LostCacher/osmofresh-quellapro-reverse-engineering/Pictures/Hauptplatine_IC1_28Pin.png

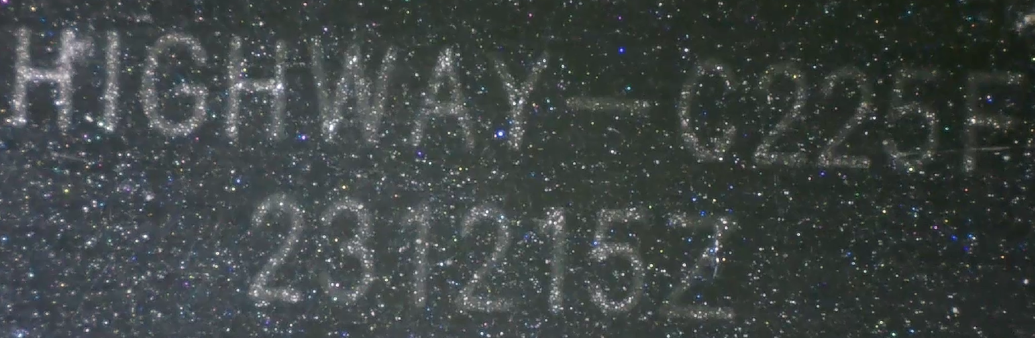
Pictures/Hauptplatine_IC1_28Pin.png
