LostCacher/osmofresh-quellapro-reverse-engineering/Pictures/Hauptplatine_U4_16Pin.png

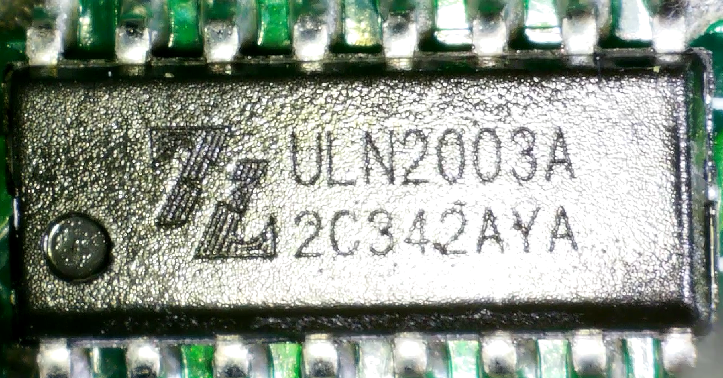
Pictures/Hauptplatine_U4_16Pin.png
