LostCacher/osmofresh-quellapro-reverse-engineering/KiCAD/OsmoFresh_Quella_PRO/MainPCB.5Vdc.kicad_sch

## KiCad design KiCAD/OsmoFresh_Quella_PRO/MainPCB.5Vdc.kicad_sch (2026-08-21, an earlier design)

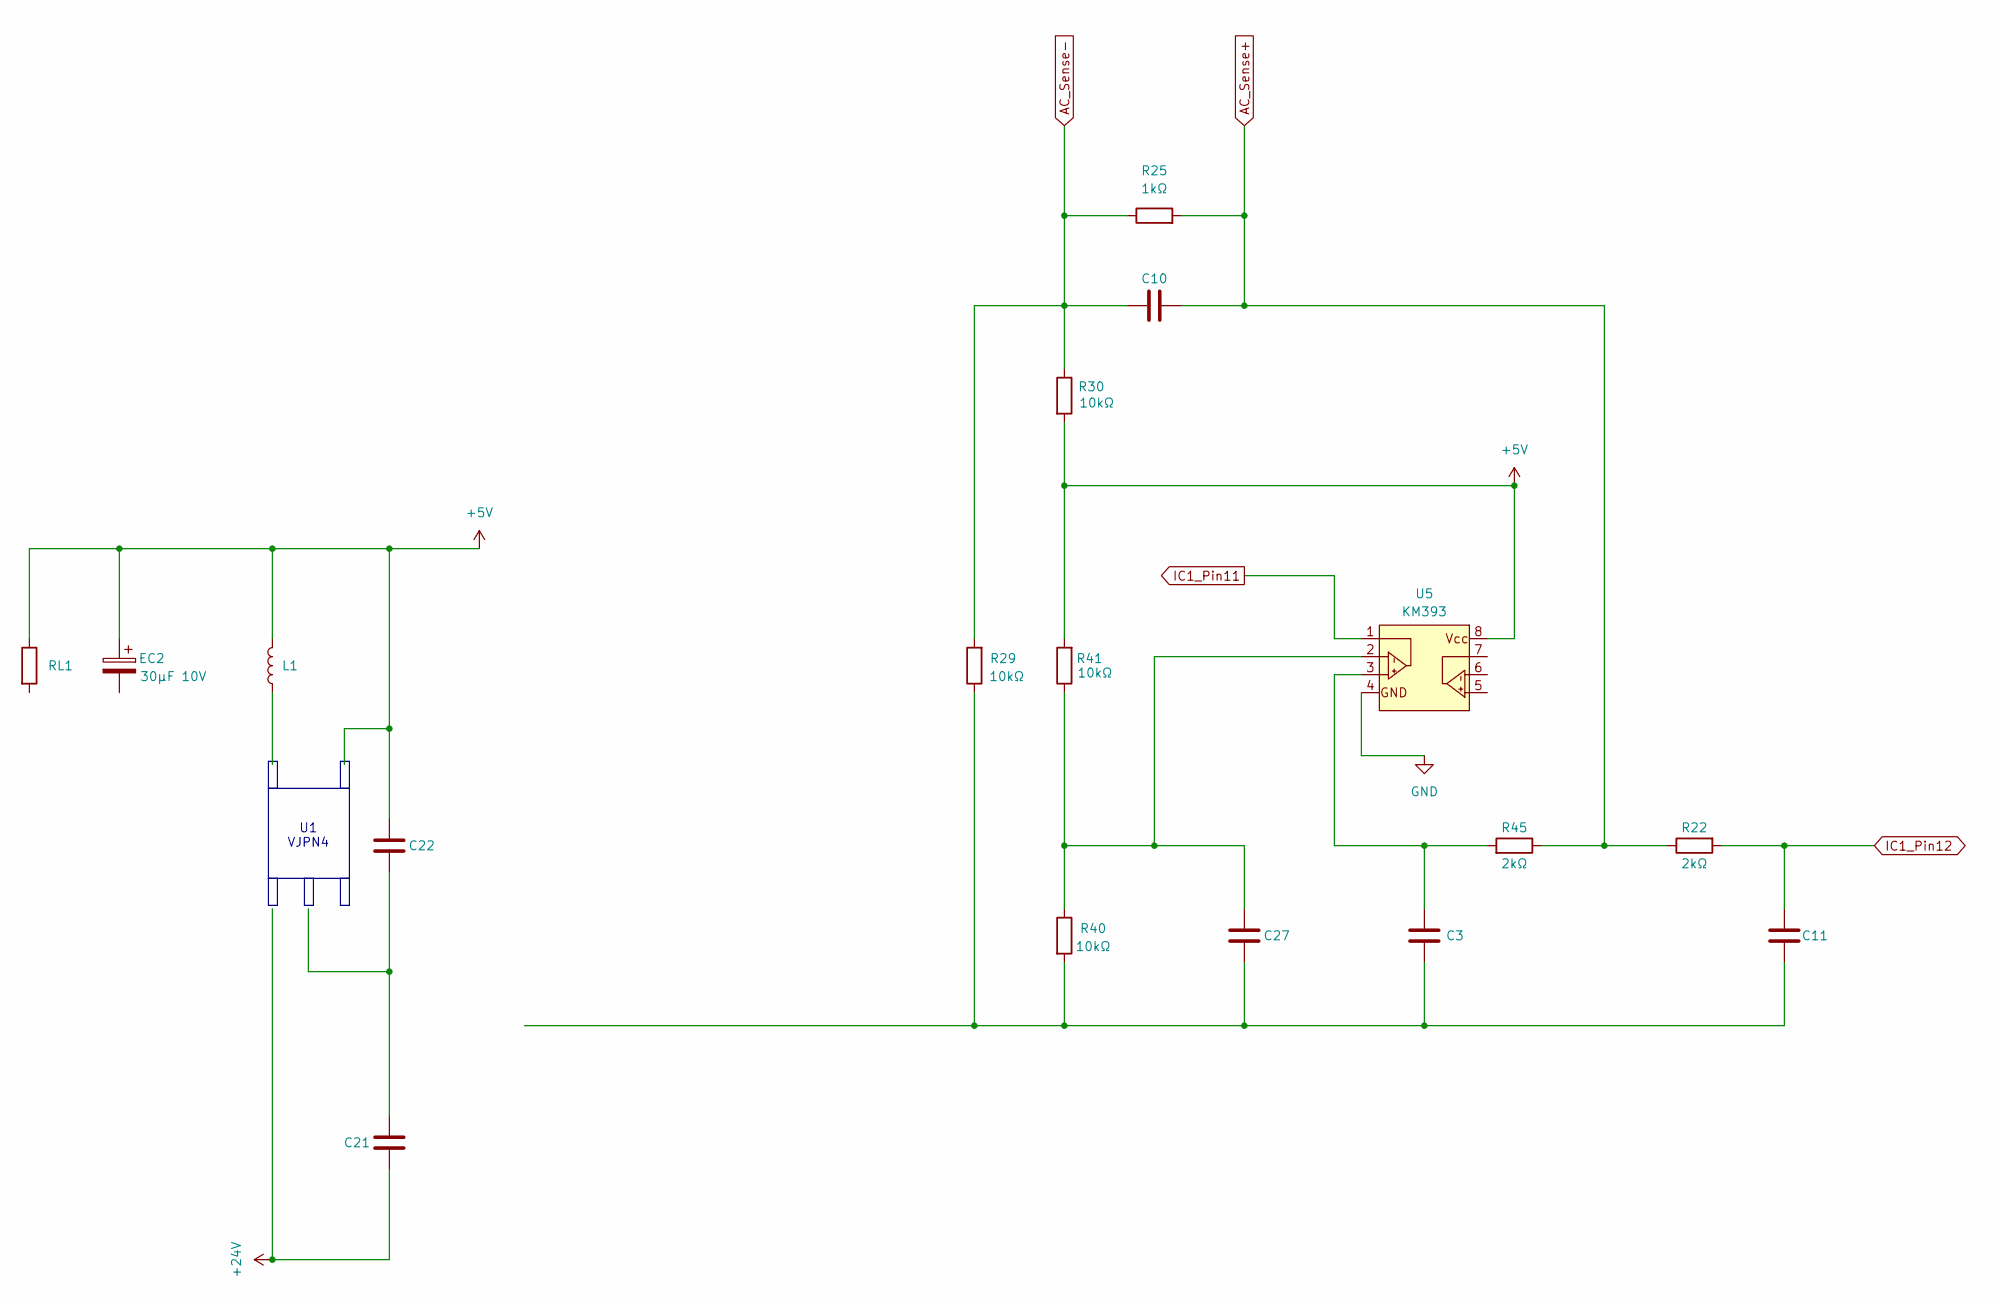
[picture p14: schematic MainPCB.5Vdc.kicad_sch]

Parts:
C3, C11: C
C10, C21, C22, C27: unkown
EC2: 30µF 10V
L1: (no value)
R22, R45: 2kΩ
R25: 1kΩ
R29, R30, R40, R41: 10kΩ
RL1: (no value)
U5: KM393

Connections:
+5V: C22.2, EC2.1, L1.2, R30.2, R41.2, RL1.1, U5.8
+24V: C21.2
AC_Sense+: C10.1, R22.1, R25.2, R45.1
AC_Sense-: C10.2, R25.1, R29.2, R30.1
GND: U5.4
IC1_Pin11: U5.1
IC1_Pin12: C11.1, R22.2
unnamed: C3.1, R45.2, U5.3
unnamed: C3.2, C11.2, C27.1, R29.1, R40.2
unnamed: C21.1, C22.1
unnamed: C27.2, R40.1, R41.1, U5.2

Notes on the sheet:
U1 VJPN4
