LostCacher/osmofresh-quellapro-reverse-engineering/KiCAD/OsmoFresh_Quella_PRO/MainPCB.24Vdc.kicad_sch

## KiCad design KiCAD/OsmoFresh_Quella_PRO/MainPCB.24Vdc.kicad_sch (2026-08-21, an earlier design)

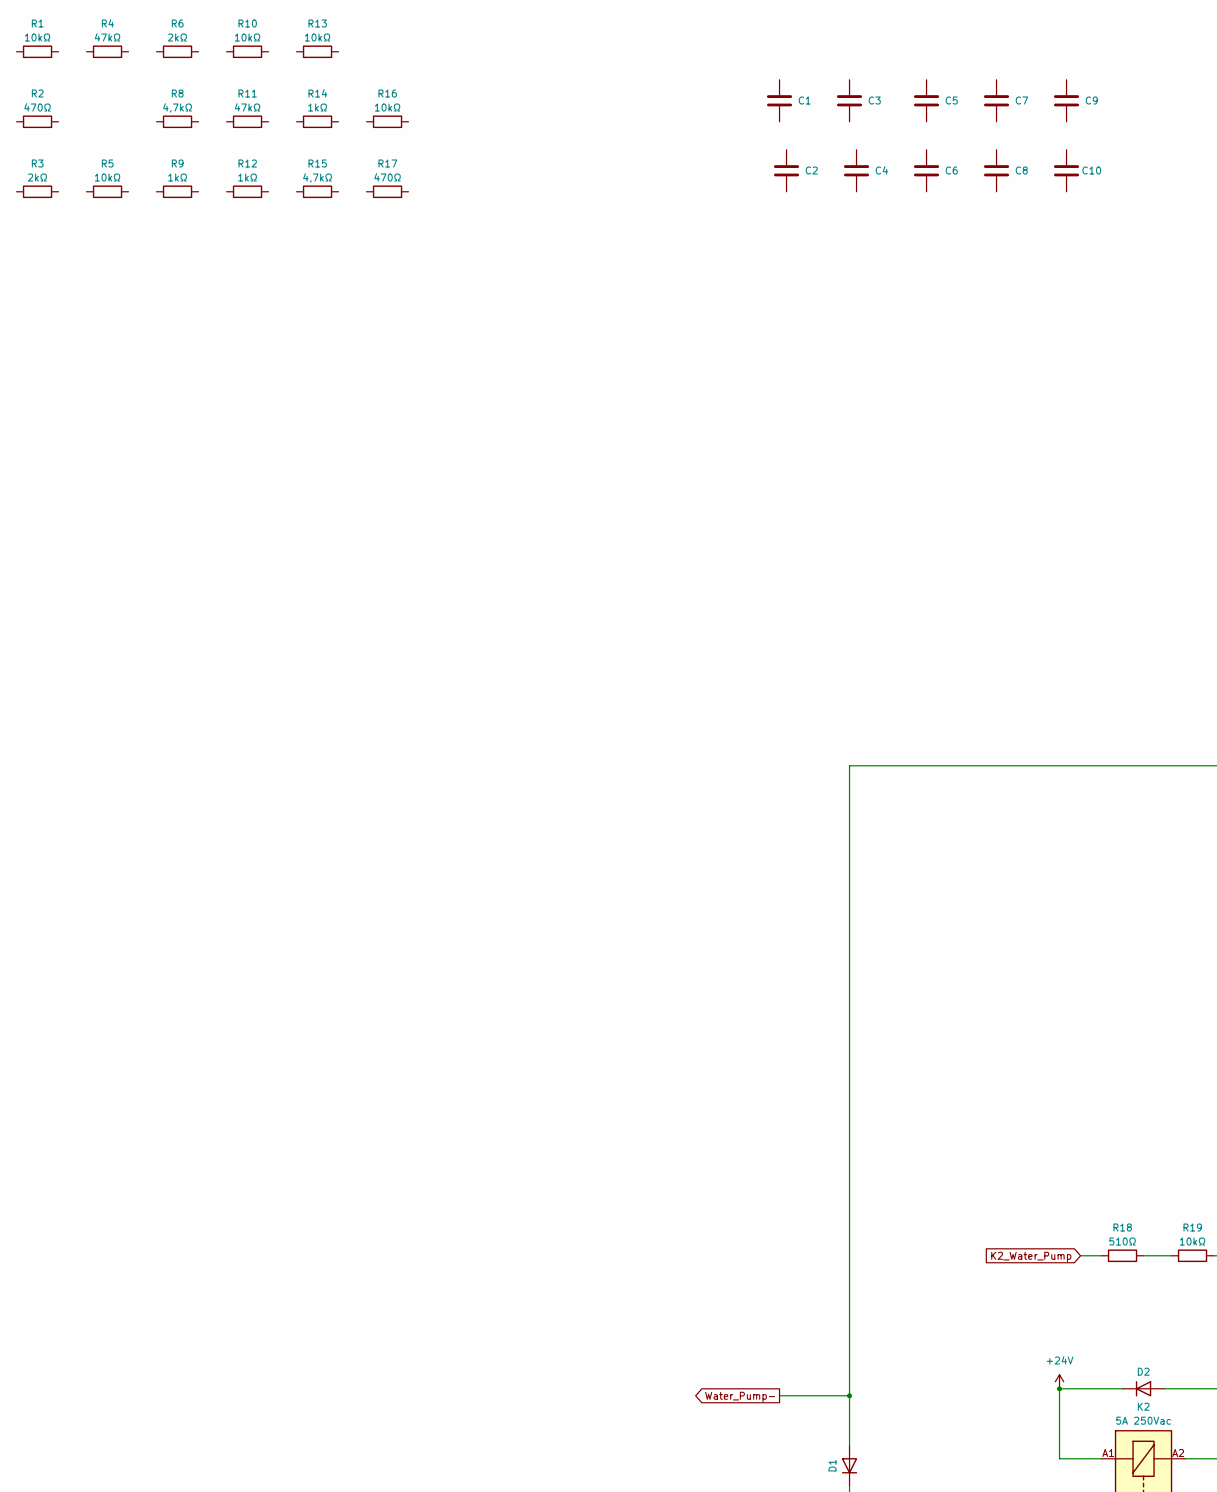
[picture p15: schematic MainPCB.24Vdc.kicad_sch, part in row 1, column 1]

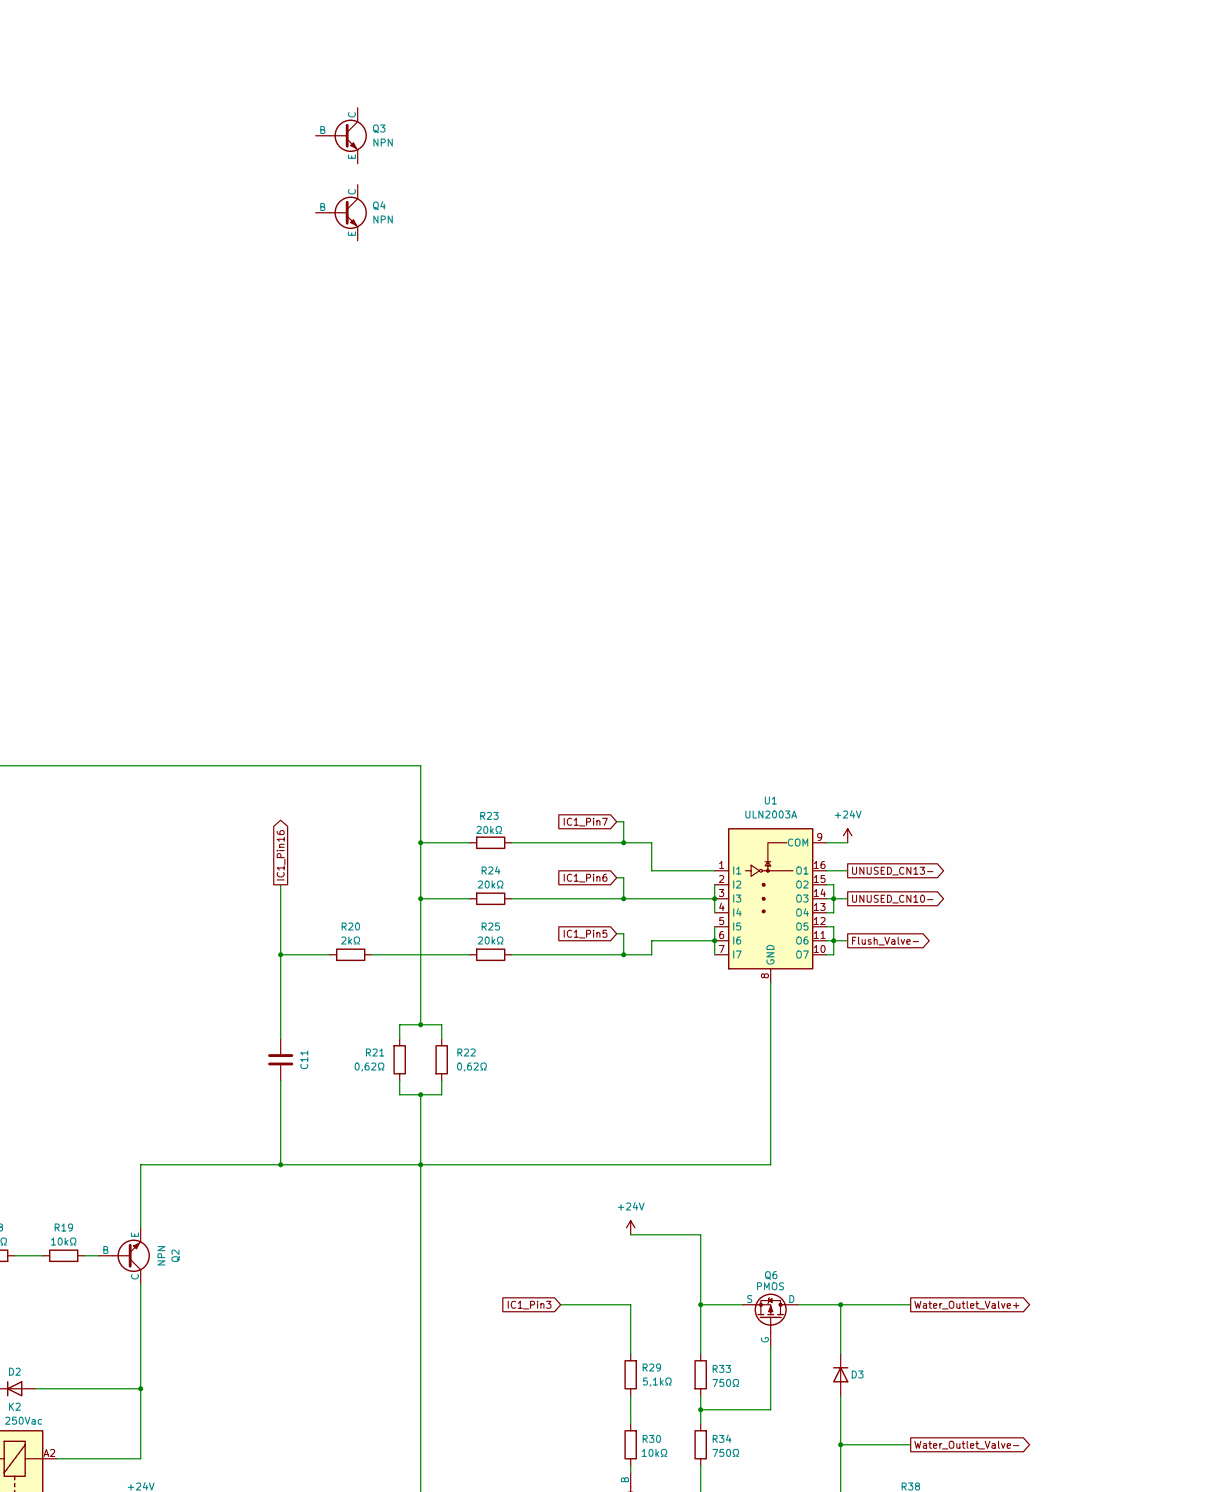
[picture p16: schematic MainPCB.24Vdc.kicad_sch, part in row 1, column 2]

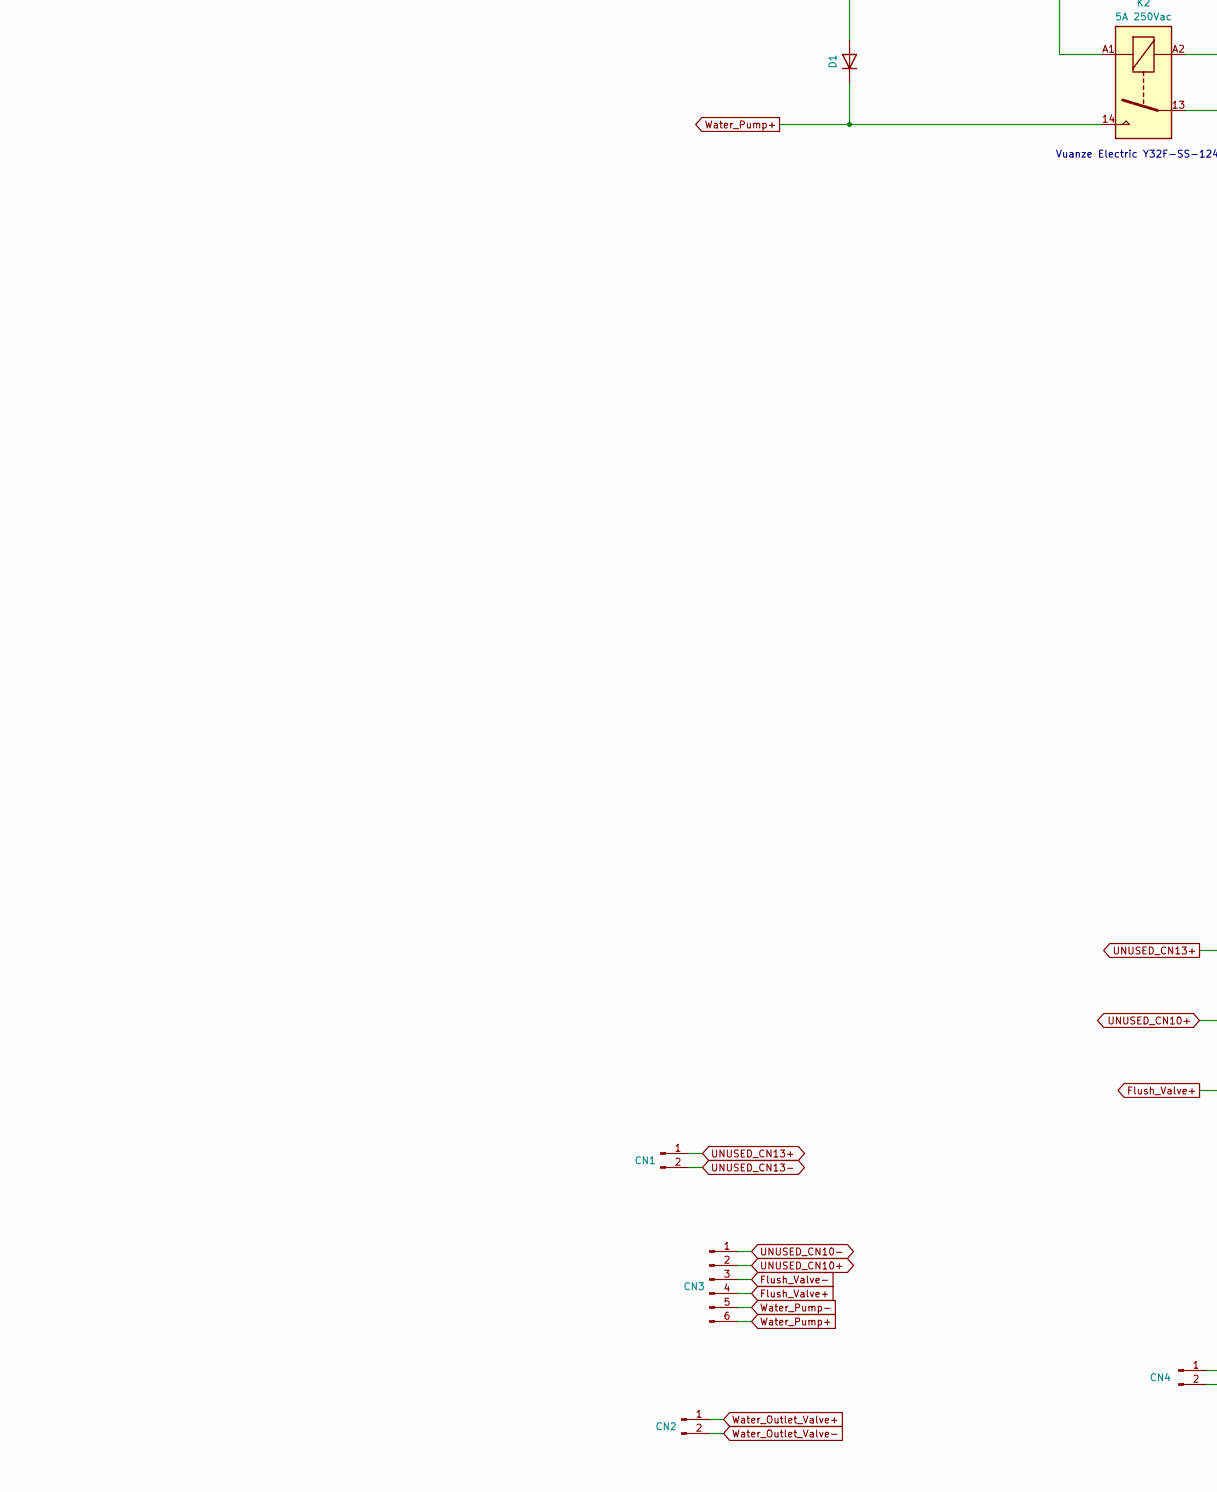
[picture p17: schematic MainPCB.24Vdc.kicad_sch, part in row 2, column 1]

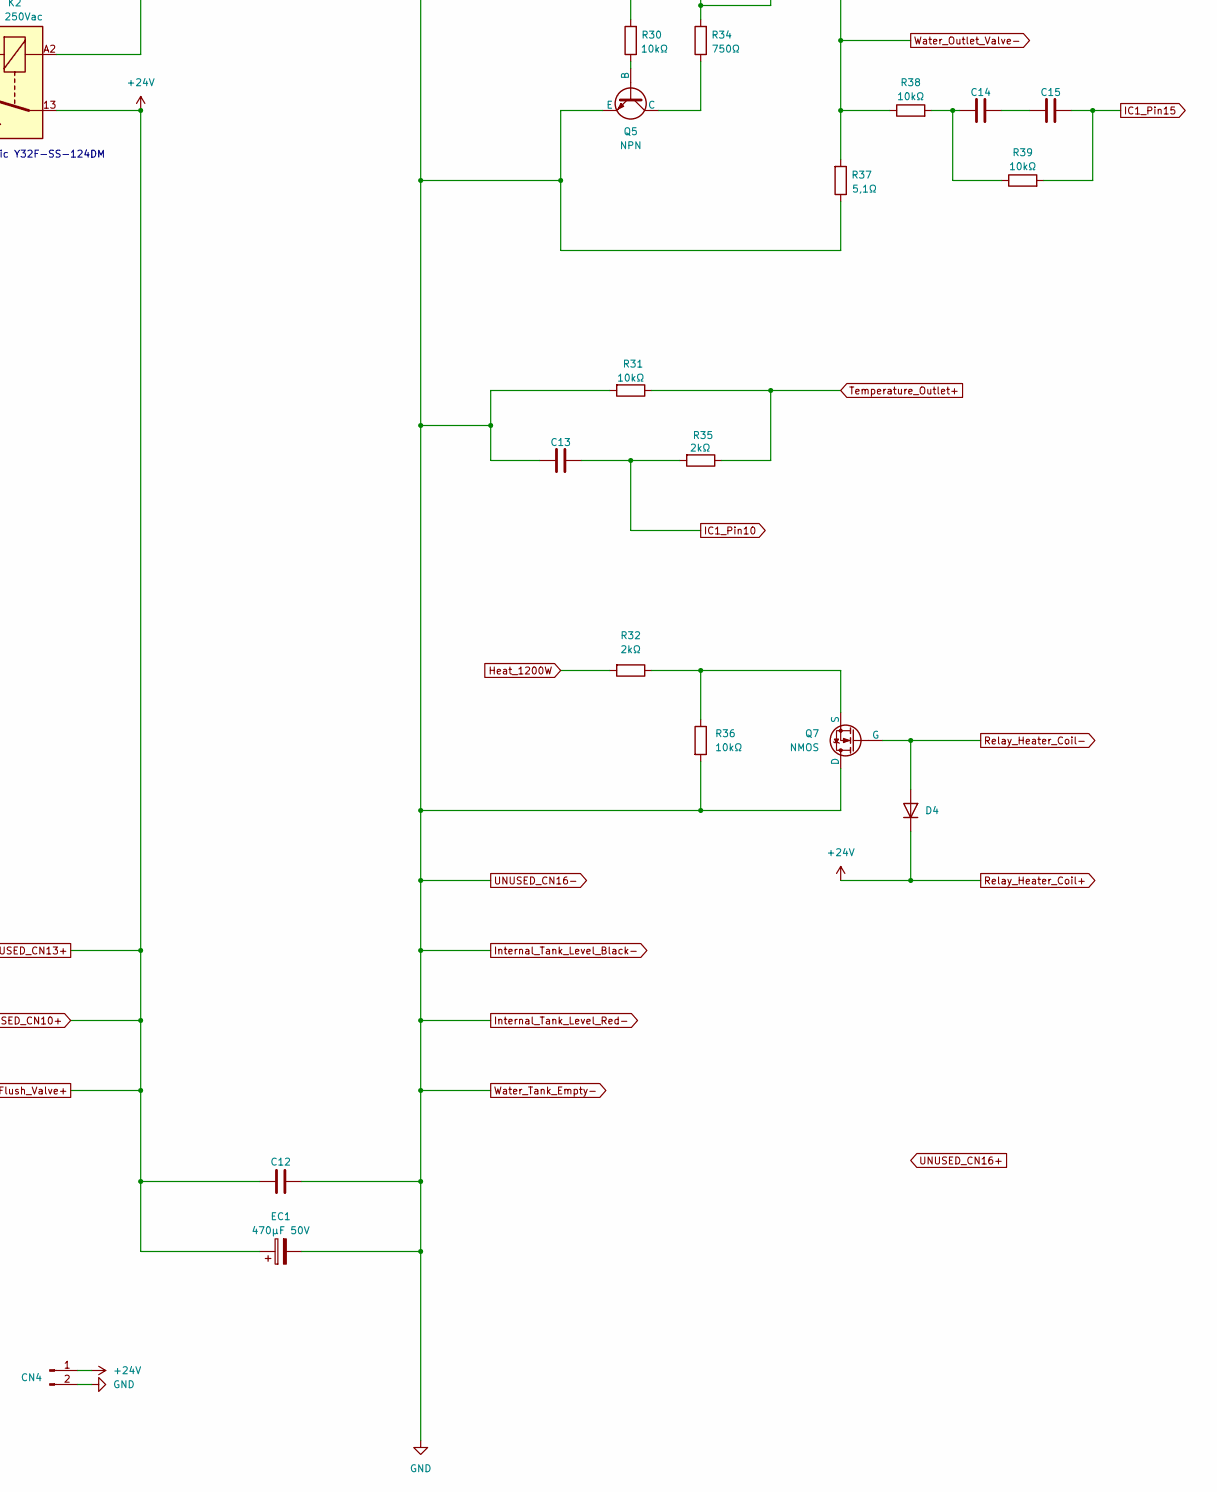
[picture p18: schematic MainPCB.24Vdc.kicad_sch, part in row 2, column 2]

Parts:
C1, C2, C3, C4, C5, C6, C7, C8, C9, C10, C13, C14, C15: unkown
C11: C
C12: (no value)
CN1, CN2, CN4: Conn_01x02_Pin
CN3: Conn_01x06_Pin
D1, D2, D3: D
D4: (no value)
EC1: 470µF 50V
K2: 5A 250Vac
Q2, Q3, Q4, Q5: NPN
Q6: PMOS
Q7: NMOS
R1, R5, R10, R13, R16, R19, R30, R31, R36, R38, R39: 10kΩ
R2, R17: 470Ω
R3, R6, R20, R32, R35: 2kΩ
R4, R11: 47kΩ
R8, R15: 4,7kΩ
R9, R12, R14: 1kΩ
R18: 510Ω
R21, R22: 0,62Ω
R23, R24, R25: 20kΩ
R29: 5,1kΩ
R33, R34: 750Ω
R37: 5,1Ω
U1: ULN2003A

Connections:
+24V: C12.1, CN1.1, CN3.2, CN3.4, CN4.1, D2.1 (K), D4.1 (K), EC1.1, K2.13, K2.A1, Q6.3 (S), R33.1, U1.9 (COM)
Flush_Valve-: CN3.3, U1.10 (O7), U1.11 (O6), U1.12 (O5)
GND: C11.1, C12.2, C13.1, CN4.2, EC1.2, Q2.3 (E), Q5.3 (E), Q7.1 (D), R21.1, R22.2, R31.2, R36.2, R37.1, U1.8 (GND)
Heat_1200W: R32.2
IC1_Pin3: R29.2
IC1_Pin5: R25.1, U1.5 (I5), U1.6 (I6), U1.7 (I7)
IC1_Pin6: R24.1, U1.2 (I2), U1.3 (I3), U1.4 (I4)
IC1_Pin7: R23.1, U1.1 (I1)
IC1_Pin10: C13.2, R35.2
IC1_Pin15: C15.1, R39.2
IC1_Pin16: C11.2, R20.2
K2_Water_Pump: R18.1
unnamed: C14.1, C15.2
unnamed: C14.2, R38.2, R39.1
unnamed: D2.2 (A), K2.A2, Q2.1 (C)
unnamed: Q2.2 (B), R19.2
unnamed: Q5.1 (C), R34.1
unnamed: Q5.2 (B), R30.1
unnamed: Q6.2 (G), R33.2, R34.2
unnamed: Q7.3 (S), R32.1, R36.1
unnamed: R18.2, R19.1
unnamed: R20.1, R25.2
unnamed: R29.1, R30.2
Relay_Heater_Coil-: D4.2 (A), Q7.2 (G)
Temperature_Outlet+: R31.1, R35.1
UNUSED_CN10-: CN3.1, U1.13 (O4), U1.14 (O3), U1.15 (O2)
UNUSED_CN13-: CN1.2, U1.16 (O1)
Water_Outlet_Valve+: CN2.1, D3.1 (K), Q6.1 (D)
Water_Outlet_Valve-: CN2.2, D3.2 (A), R37.2, R38.1
Water_Pump+: CN3.6, D1.1 (K), K2.14
Water_Pump-: CN3.5, D1.2 (A), R21.2, R22.1, R23.2, R24.2

Notes on the sheet:
Vuanze Electric Y32F-SS-124DM
