LostCacher/osmofresh-quellapro-reverse-engineering/KiCAD/OsmoFresh_Quella_PRO/MainPCB.+24Vdc.kicad_sch

## KiCad design KiCAD/OsmoFresh_Quella_PRO/MainPCB.+24Vdc.kicad_sch (2026-08-15, an earlier design)

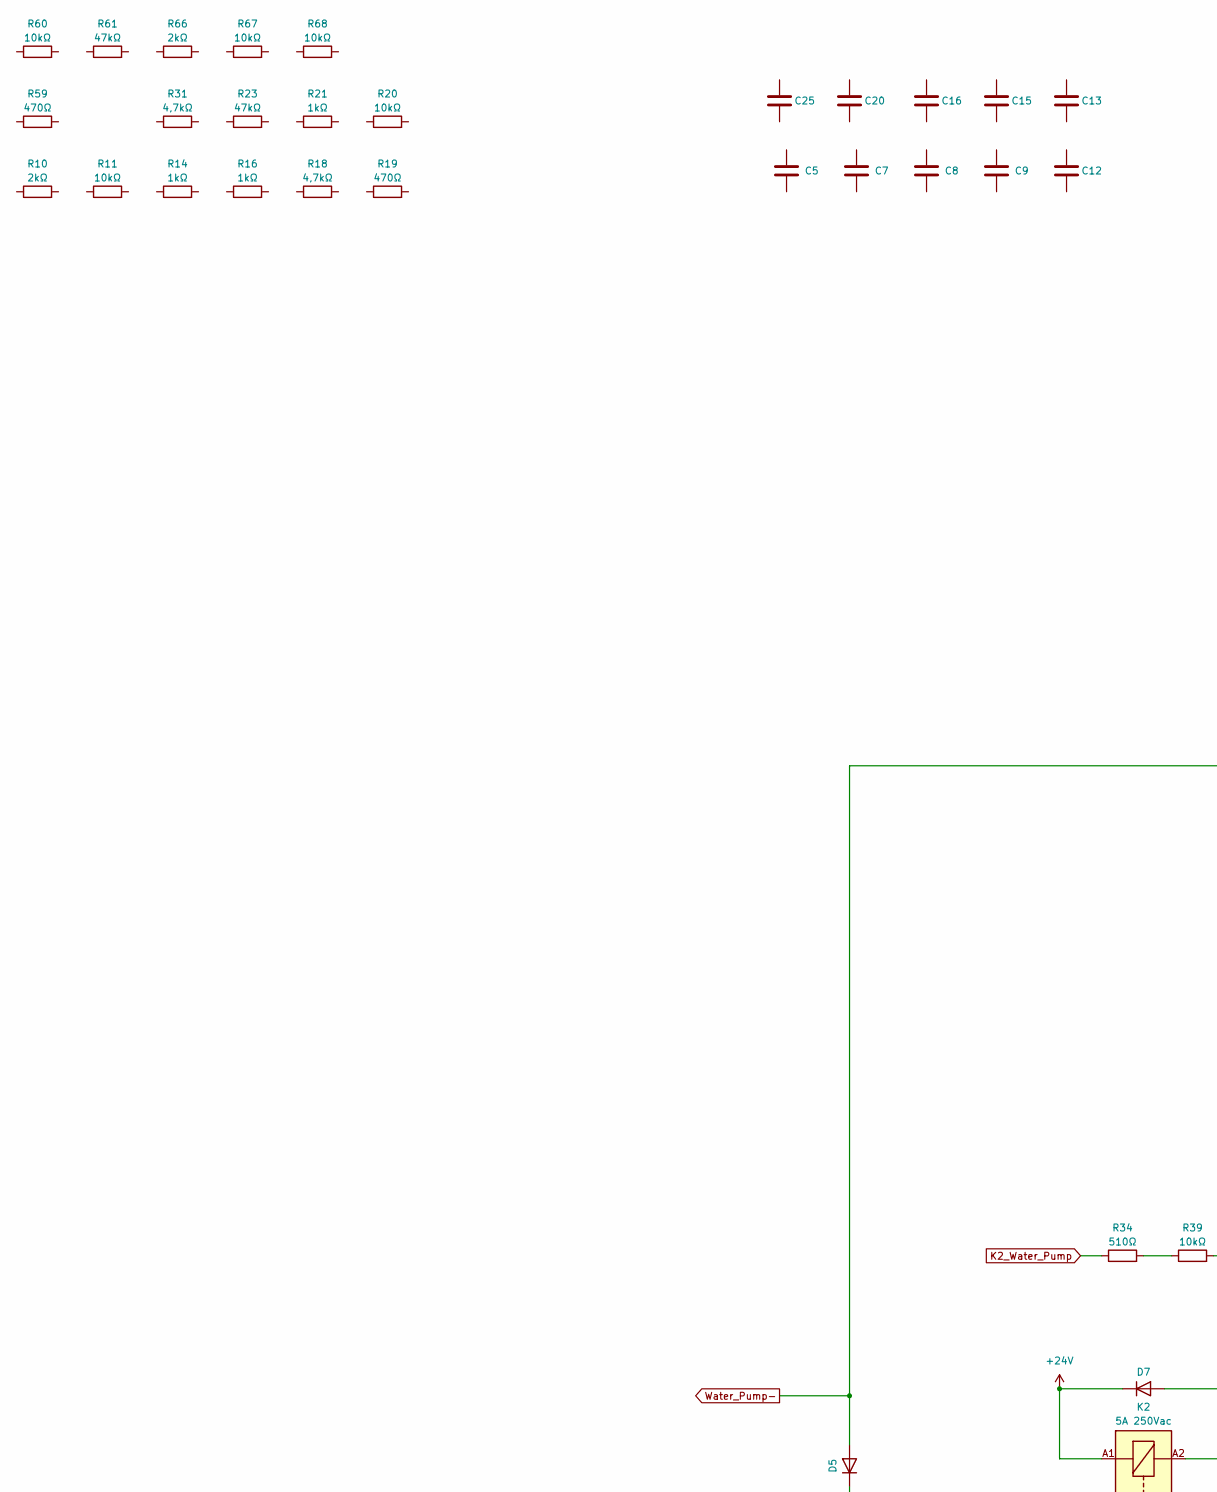
[picture p19: schematic MainPCB.+24Vdc.kicad_sch, part in row 1, column 1]

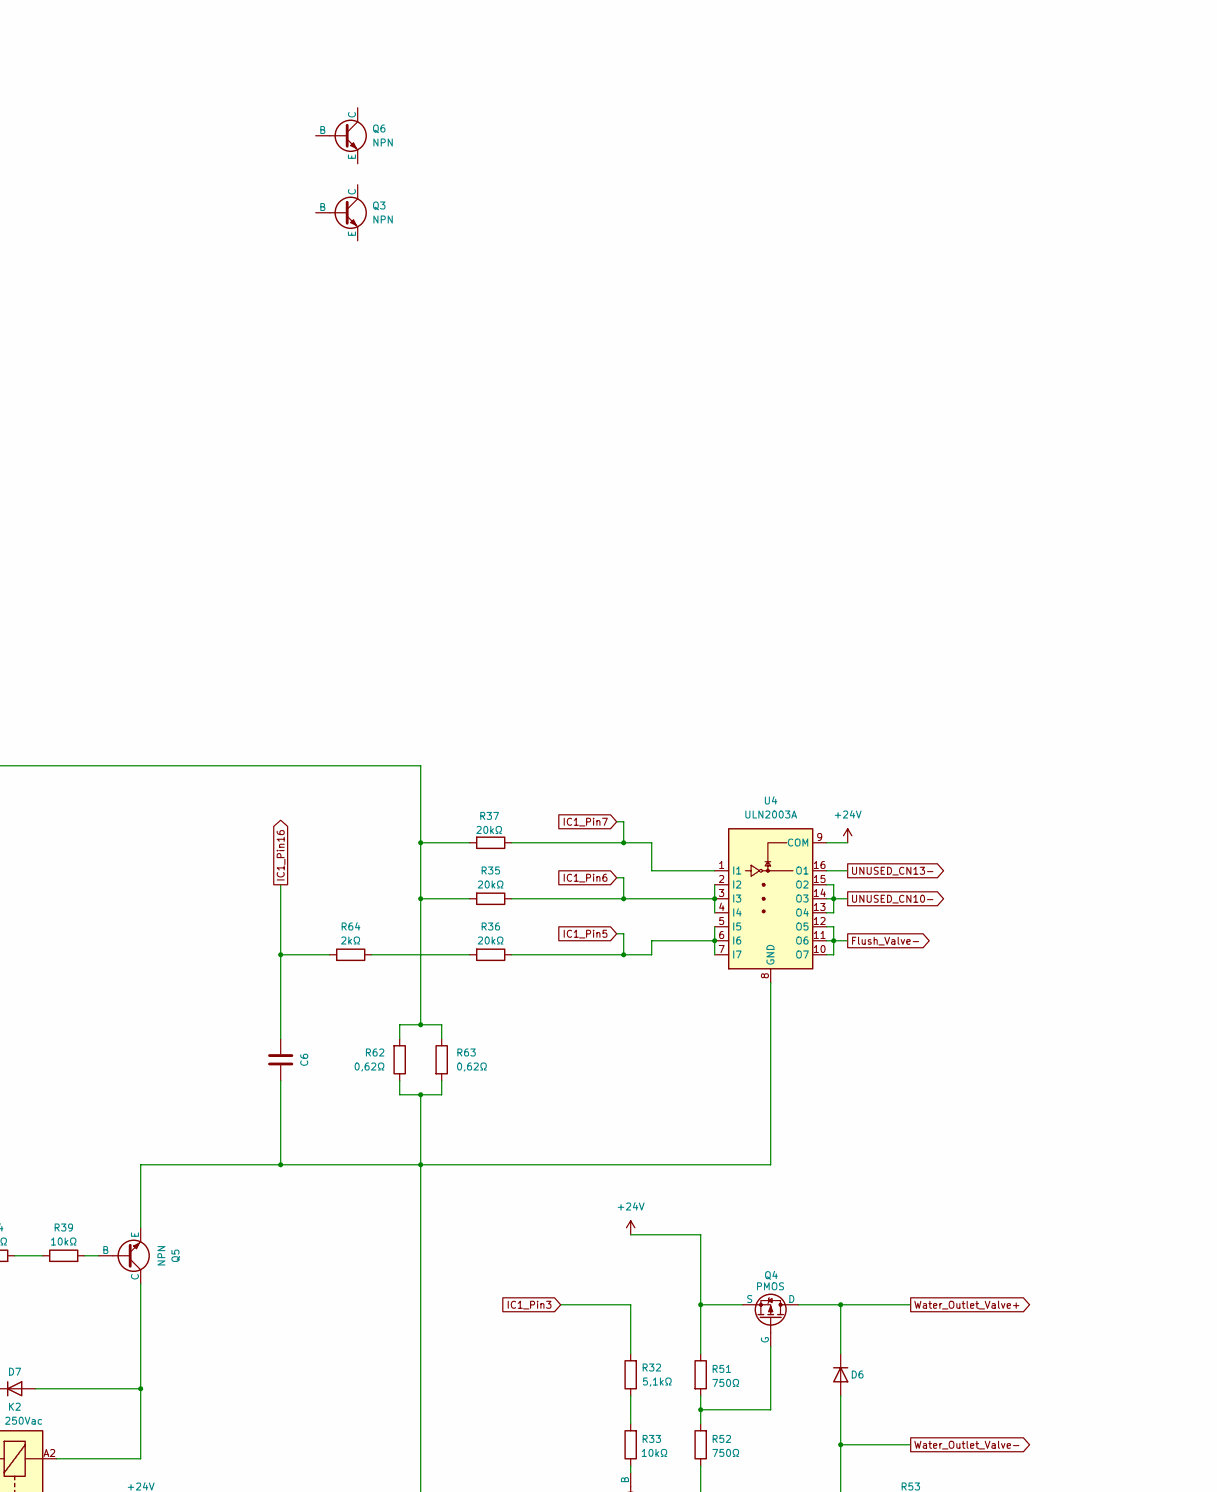
[picture p20: schematic MainPCB.+24Vdc.kicad_sch, part in row 1, column 2]

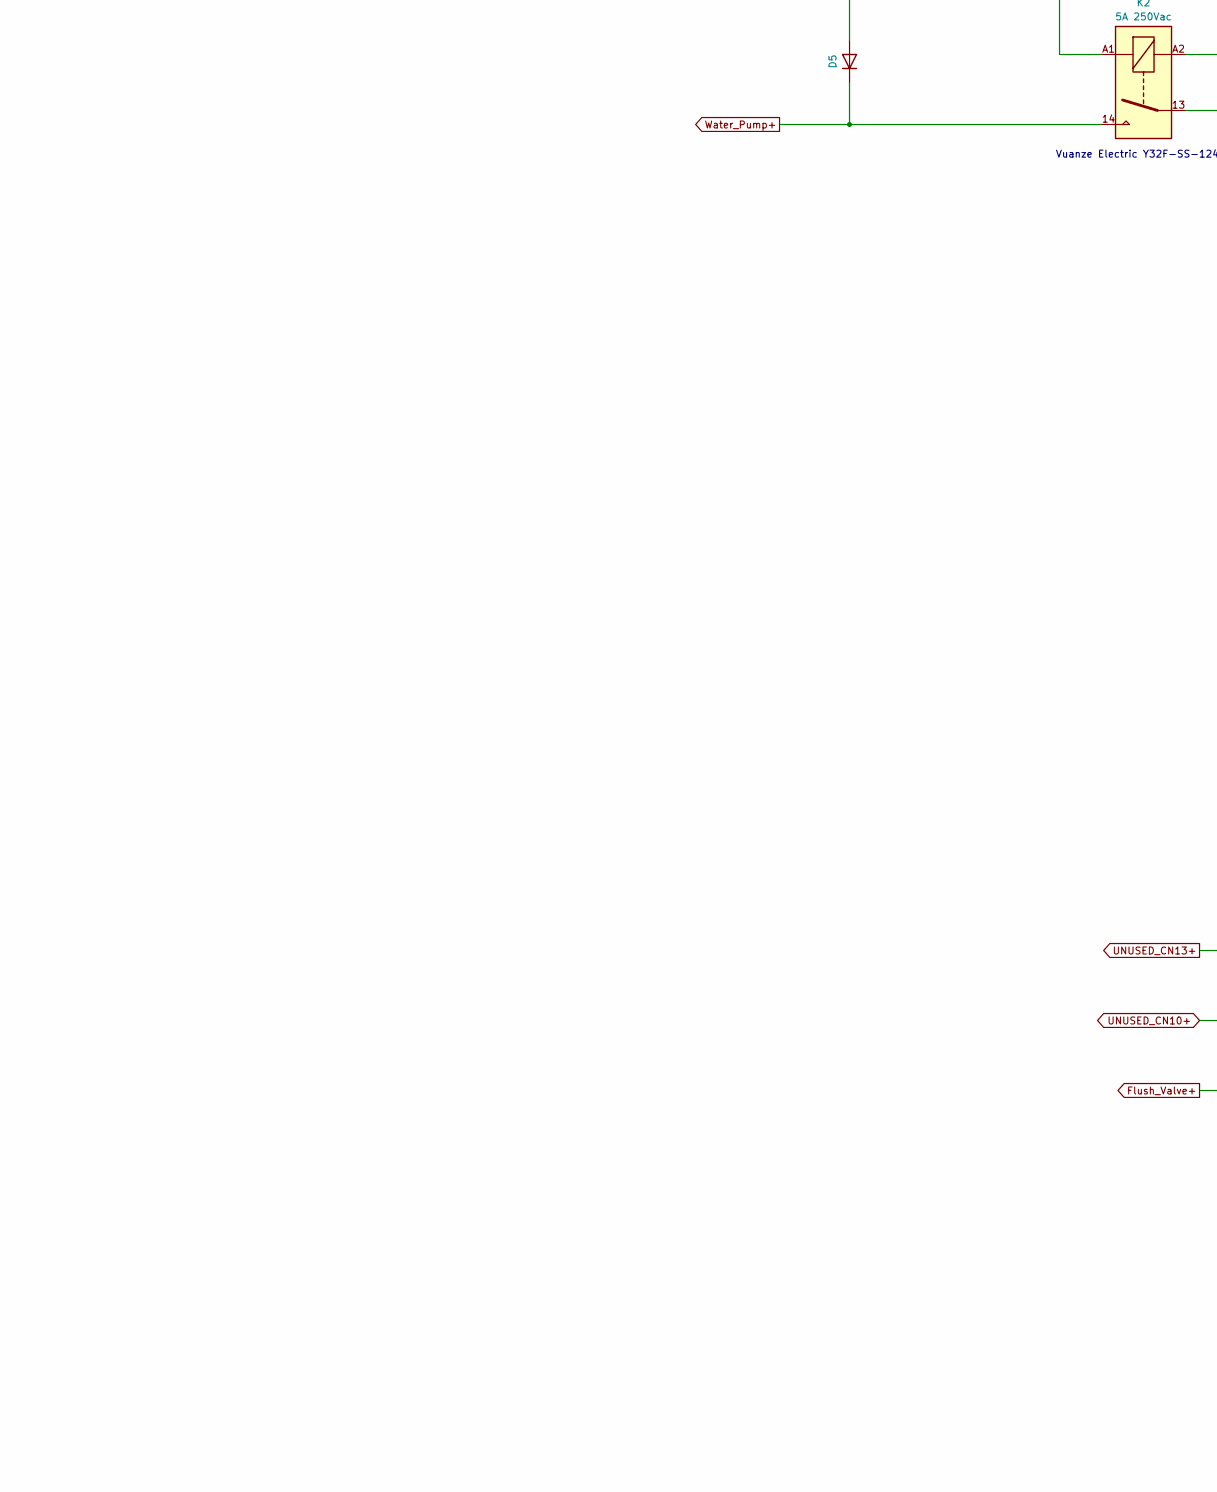
[picture p21: schematic MainPCB.+24Vdc.kicad_sch, part in row 2, column 1]

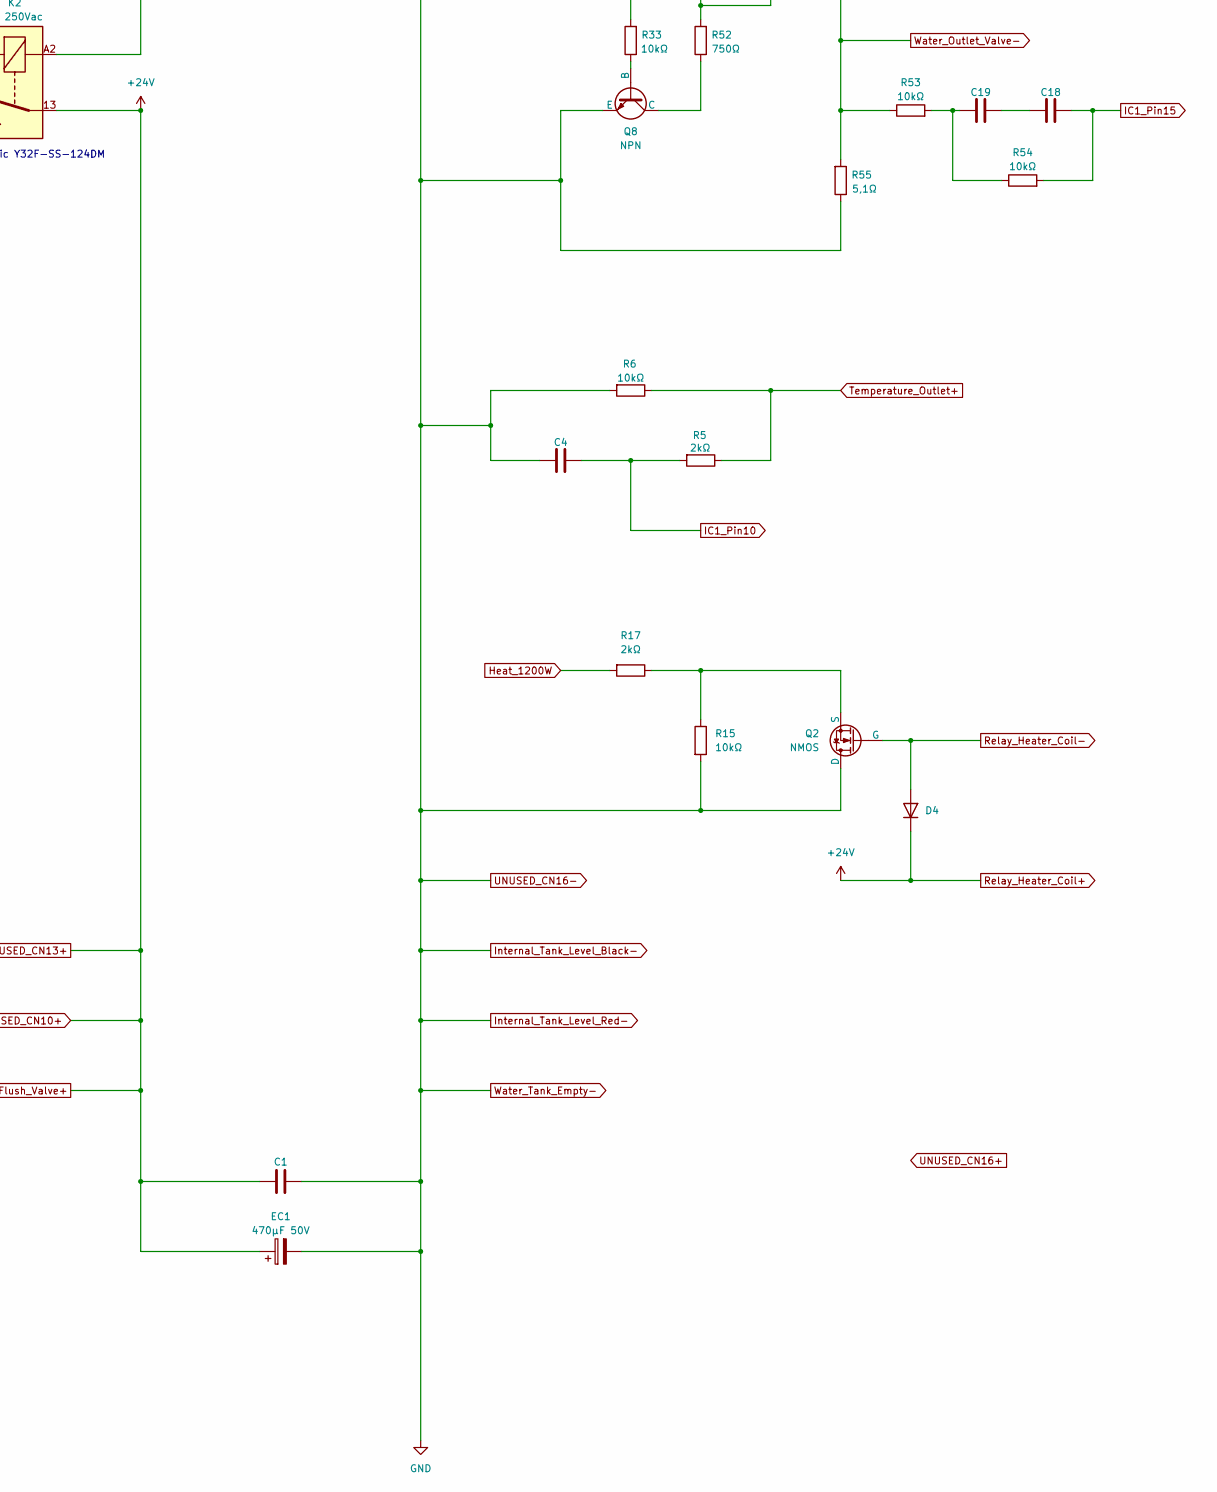
[picture p22: schematic MainPCB.+24Vdc.kicad_sch, part in row 2, column 2]

Parts:
C1: (no value)
C4, C5, C7, C8, C9, C12, C13, C15, C16, C18, C19, C20, C25: unkown
C6: C
D4: (no value)
D5, D6, D7: D
EC1: 470µF 50V
K2: 5A 250Vac
Q2: NMOS
Q3, Q5, Q6, Q8: NPN
Q4: PMOS
R5, R10, R17, R64, R66: 2kΩ
R6, R11, R15, R20, R33, R39, R53, R54, R60, R67, R68: 10kΩ
R14, R16, R21: 1kΩ
R18, R31: 4,7kΩ
R19, R59: 470Ω
R23, R61: 47kΩ
R32: 5,1kΩ
R34: 510Ω
R35, R36, R37: 20kΩ
R51, R52: 750Ω
R55: 5,1Ω
R62, R63: 0,62Ω
U4: ULN2003A

Connections:
+24V: C1.1, D4.1 (K), D7.1 (K), EC1.1, K2.13, K2.A1, Q4.3 (S), R51.1, U4.9 (COM)
Flush_Valve-: U4.10 (O7), U4.11 (O6), U4.12 (O5)
GND: C1.2, C4.1, C6.1, EC1.2, Q2.1 (D), Q5.3 (E), Q8.3 (E), R6.2, R15.2, R55.1, R62.1, R63.2, U4.8 (GND)
Heat_1200W: R17.2
IC1_Pin3: R32.2
IC1_Pin5: R36.1, U4.5 (I5), U4.6 (I6), U4.7 (I7)
IC1_Pin6: R35.1, U4.2 (I2), U4.3 (I3), U4.4 (I4)
IC1_Pin7: R37.1, U4.1 (I1)
IC1_Pin10: C4.2, R5.2
IC1_Pin15: C18.1, R54.2
IC1_Pin16: C6.2, R64.2
K2_Water_Pump: R34.1
unnamed: C18.2, C19.1
unnamed: C19.2, R53.2, R54.1
unnamed: D7.2 (A), K2.A2, Q5.1 (C)
unnamed: Q2.3 (S), R15.1, R17.1
unnamed: Q4.2 (G), R51.2, R52.2
unnamed: Q5.2 (B), R39.2
unnamed: Q8.1 (C), R52.1
unnamed: Q8.2 (B), R33.1
unnamed: R32.1, R33.2
unnamed: R34.2, R39.1
unnamed: R36.2, R64.1
Relay_Heater_Coil-: D4.2 (A), Q2.2 (G)
Temperature_Outlet+: R5.1, R6.1
UNUSED_CN10-: U4.13 (O4), U4.14 (O3), U4.15 (O2)
UNUSED_CN13-: U4.16 (O1)
Water_Outlet_Valve+: D6.1 (K), Q4.1 (D)
Water_Outlet_Valve-: D6.2 (A), R53.1, R55.2
Water_Pump+: D5.1 (K), K2.14
Water_Pump-: D5.2 (A), R35.2, R37.2, R62.2, R63.1

Notes on the sheet:
Vuanze Electric Y32F-SS-124DM
