LostCacher/osmofresh-quellapro-reverse-engineering/KiCAD/OsmoFresh_Quella_PRO/MainPCB.MCU.kicad_sch

## KiCad design KiCAD/OsmoFresh_Quella_PRO/MainPCB.MCU.kicad_sch (2026-08-21, an earlier design)

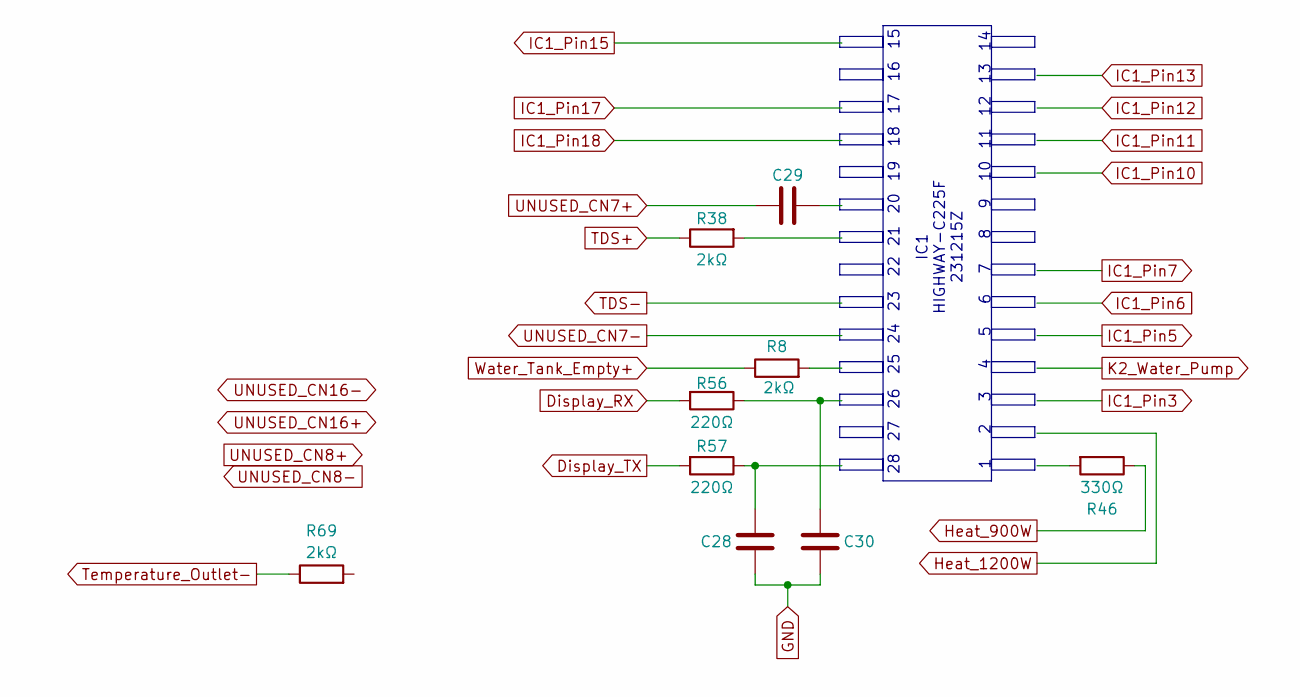
[picture p23: schematic MainPCB.MCU.kicad_sch]

Parts:
C28, C29, C30: unkown
R8, R38, R69: 2kΩ
R46: 330Ω
R56, R57: 220Ω

Connections:
Display_RX: R56.2
Display_TX: R57.2
GND: C28.1, C30.1
Heat_900W: R46.1
unnamed: C28.2, R57.1
unnamed: C30.2, R56.1
TDS+: R38.1
Temperature_Outlet-: R69.1
UNUSED_CN7+: C29.2
Water_Tank_Empty+: R8.1

Notes on the sheet:
IC1 HIGHWAY-C225F 231215Z
