LostCacher/osmofresh-quellapro-reverse-engineering/KiCAD/OsmoFresh_Quella_PRO/OsmoFresh_Quella_PRO.kicad_sch

## KiCad design KiCAD/OsmoFresh_Quella_PRO/OsmoFresh_Quella_PRO.kicad_sch (2026-08-21, an earlier design)

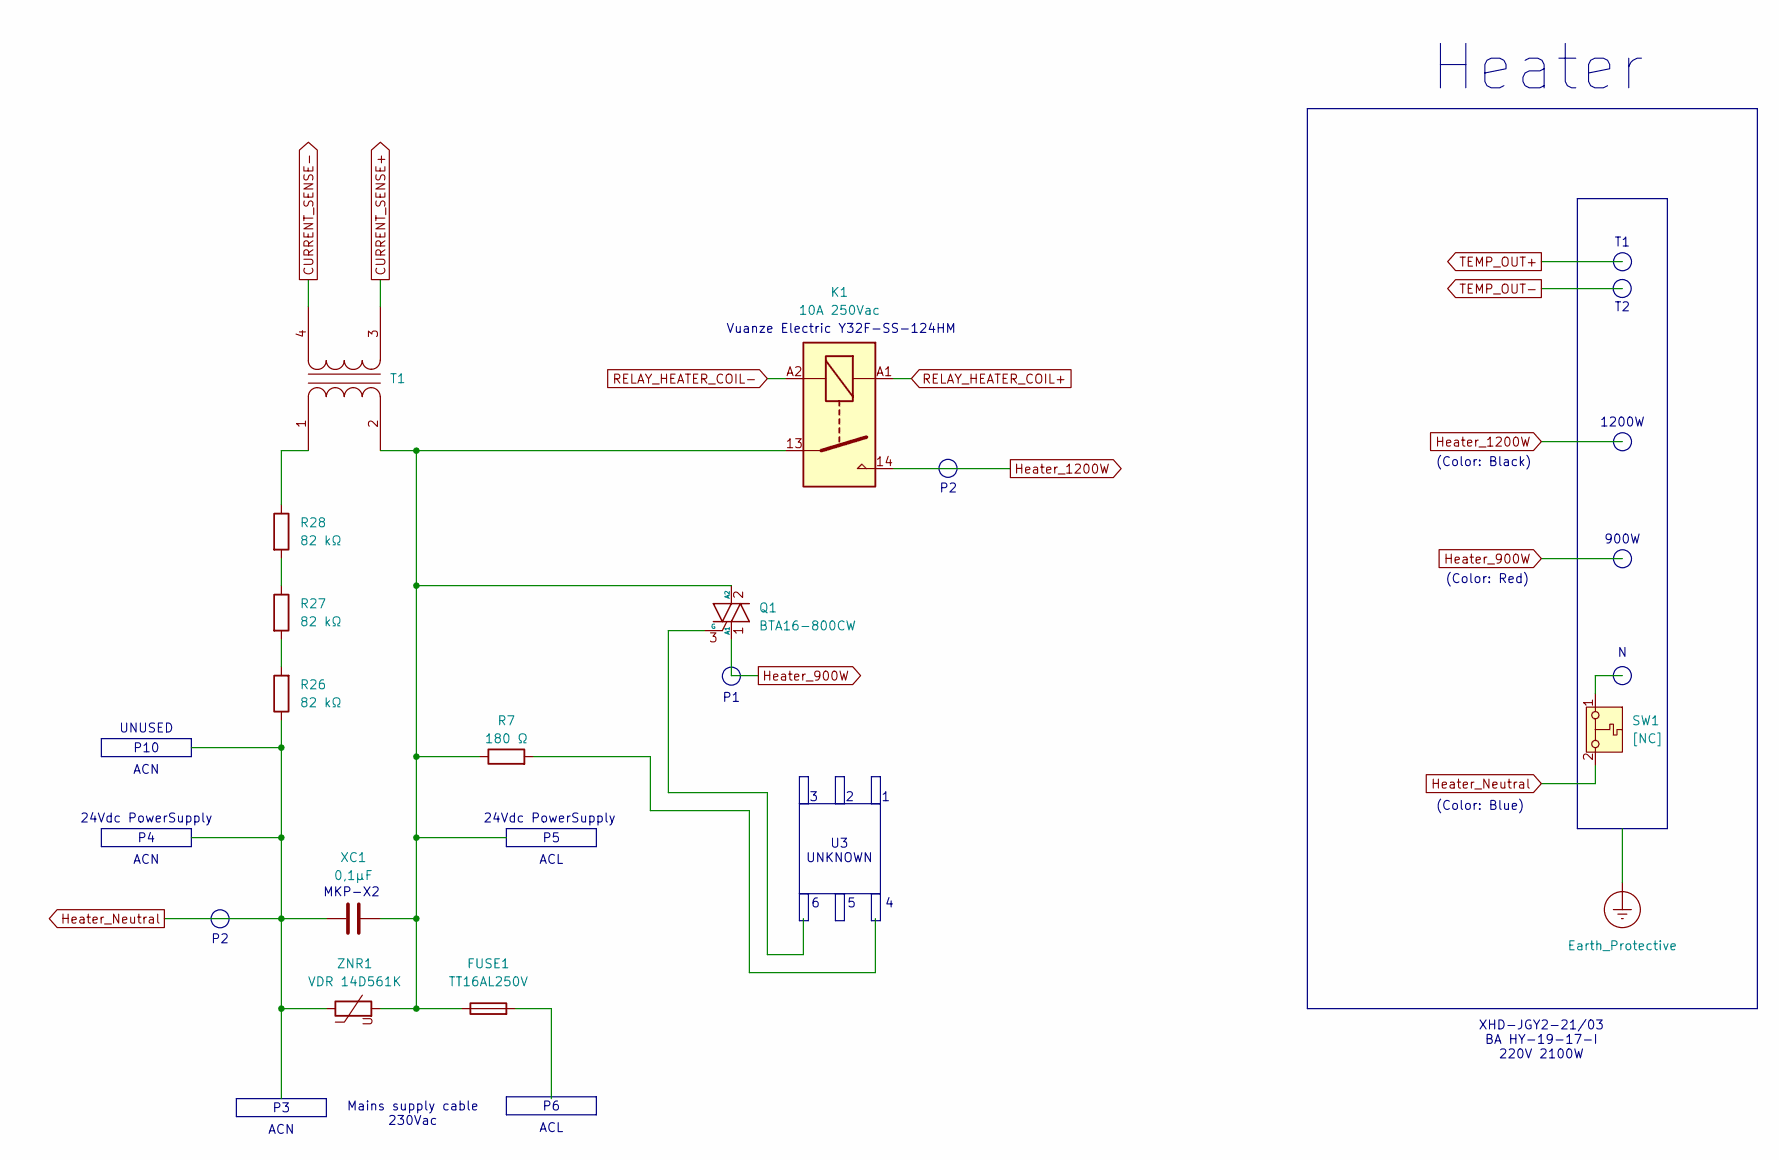
[picture p24: schematic OsmoFresh_Quella_PRO.kicad_sch]

Parts:
FUSE1: TT16AL250V
K1: 10A 250Vac
Q1: BTA16-800CW; TO-220-3_Vertical
R7: 180 Ω
R26, R27, R28: 82 kΩ
SW1: [NC]
T1: (no value)
XC1: 0,1µF
ZNR1: VDR 14D561K

Connections:
CURRENT_SENSE+: T1.3 (SA)
CURRENT_SENSE-: T1.4 (SB)
Heater_900W: Q1.1 (A1)
Heater_1200W: K1.14
Heater_Neutral: R26.1, SW1.2, XC1.1, ZNR1.1
unnamed: FUSE1.1, K1.13, Q1.2 (A2), R7.1, T1.2 (AB), XC1.2, ZNR1.2
unnamed: R26.2, R27.2
unnamed: R27.1, R28.2
unnamed: R28.1, T1.1 (AA)
RELAY_HEATER_COIL+: K1.A1
RELAY_HEATER_COIL-: K1.A2

Notes on the sheet:
900W
1200W
ACL
24Vdc PowerSupply
ACN
MKP-X2
Mains supply cable 230Vac
U3 UNKNOWN
Heater
Vuanze Electric Y32F-SS-124HM
P10
UNUSED
(Color: Red)
XHD-JGY2-21/03 BA HY-19-17-I 220V 2100W
(Color: Black)
(Color: Blue)
