LostCacher/osmofresh-quellapro-reverse-engineering/KiCAD/OsmoFresh_Quella_PRO/mainpcb.secondary.kicad_sch

## KiCad design KiCAD/OsmoFresh_Quella_PRO/mainpcb.secondary.kicad_sch (2026-08-21, an earlier design)

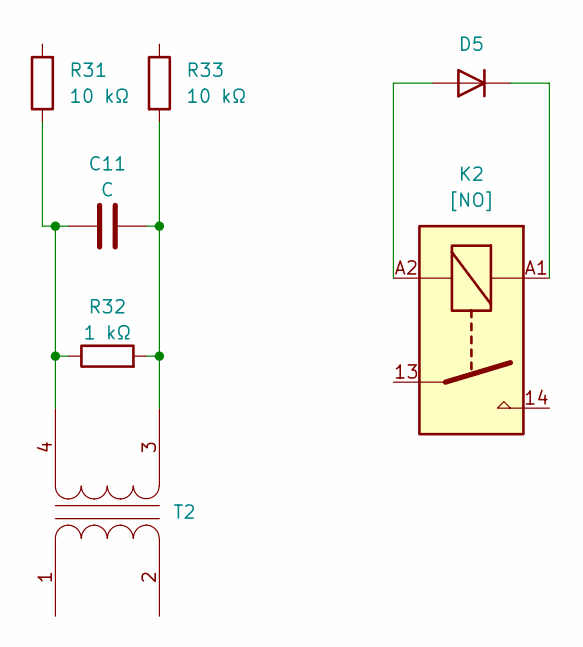
[picture p25: schematic mainpcb.secondary.kicad_sch]

Parts:
C11: C
D5: (no value)
K2: [NO]
R31, R33: 10 kΩ
R32: 1 kΩ
T2: (no value)

Connections:
unnamed: C11.1, R31.1, R32.1, T2.4 (SB)
unnamed: C11.2, R32.2, R33.2, T2.3 (SA)
unnamed: D5.1 (K), K2.A1
unnamed: D5.2 (A), K2.A2
